salvogendut/goodjohn/src/tusb_config.h

#ifndef GOODJOHN_TUSB_CONFIG_H
#define GOODJOHN_TUSB_CONFIG_H

#ifndef CFG_TUSB_MCU
#define CFG_TUSB_MCU OPT_MCU_RP2040
#endif
#ifndef CFG_TUSB_OS
#define CFG_TUSB_OS OPT_OS_PICO
#endif
#define CFG_TUSB_RHPORT0_MODE (OPT_MODE_DEVICE | OPT_MODE_FULL_SPEED)
#define CFG_TUD_ENABLED 1
#define CFG_TUD_ENDPOINT0_SIZE 64
#define CFG_TUD_HID 1
#define CFG_TUD_HID_EP_BUFSIZE 8
#define CFG_TUD_CDC 0
#define CFG_TUD_MSC 0
#define CFG_TUD_MIDI 0
#define CFG_TUD_VENDOR 0

#endif
